sparkplug619/esp32_xiaomi_m365/esp32_m365_oled/include/ARIALN9pt7b.h

const uint8_t ARIALN9pt7bBitmaps[] PROGMEM = {
  0xFF, 0xF5, 0x50, 0xC0, 0xBB, 0xAA, 0xA0, 0x12, 0x12, 0x12, 0x22, 0xFF,
  0x24, 0x24, 0x24, 0xFF, 0x44, 0x4C, 0x48, 0x48, 0x20, 0xF3, 0xB5, 0x2A,
  0x14, 0x38, 0x1C, 0x2C, 0x4A, 0x95, 0x2E, 0xCF, 0x08, 0x10, 0x60, 0x92,
  0x22, 0x44, 0x49, 0x09, 0x21, 0x28, 0x19, 0x30, 0x29, 0x09, 0x21, 0x24,
  0x44, 0x88, 0x92, 0x0C, 0x38, 0x36, 0x11, 0x0C, 0x86, 0xC1, 0xC1, 0xC1,
  0xB6, 0x8F, 0x43, 0x21, 0x99, 0xE7, 0x90, 0xF8, 0x25, 0x2D, 0x24, 0x92,
  0x4C, 0x91, 0x20, 0x91, 0x24, 0xC9, 0x24, 0xB4, 0x94, 0x80, 0x23, 0x4C,
  0xE5, 0x00, 0x10, 0x20, 0x47, 0xF1, 0x02, 0x04, 0x00, 0xD6, 0xF0, 0xC0,
  0x11, 0x32, 0x22, 0x24, 0x44, 0x48, 0x80, 0x79, 0x38, 0x61, 0x86, 0x18,
  0x61, 0x86, 0x18, 0x53, 0x78, 0x25, 0xFA, 0x49, 0x24, 0x92, 0x3C, 0xCD,
  0x0A, 0x10, 0x20, 0xC1, 0x86, 0x18, 0x61, 0x83, 0x0F, 0xE0, 0x79, 0x9A,
  0x10, 0x20, 0x41, 0x0F, 0x06, 0x05, 0x0A, 0x16, 0x67, 0x80, 0x04, 0x18,
  0x30, 0xA1, 0x44, 0x89, 0x22, 0xC5, 0xFC, 0x10, 0x20, 0x40, 0x7C, 0x83,
  0x04, 0x0F, 0x99, 0xA1, 0x03, 0x07, 0x0A, 0x16, 0x67, 0x80, 0x38, 0x9A,
  0x14, 0x08, 0x17, 0x33, 0x42, 0x85, 0x0A, 0x12, 0x63, 0x80, 0xFE, 0x08,
  0x30, 0xC1, 0x82, 0x0C, 0x10, 0x20, 0x41, 0x83, 0x06, 0x00, 0x78, 0x9A,
  0x14, 0x28, 0x59, 0x9E, 0x66, 0x85, 0x0E, 0x16, 0x67, 0x80, 0x79, 0x9A,
  0x14, 0x28, 0x50, 0xF3, 0xBB, 0x04, 0x0A, 0x16, 0x47, 0x00, 0xC0, 0x00,
  0xC0, 0xC0, 0x00, 0xD6, 0x02, 0x18, 0x43, 0x08, 0x0C, 0x04, 0x06, 0x02,
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
  {   351,   7,  13,   9,    1,  -12 },   // 0x46 'F'
  {   363,  10,  13,  11,    1,  -12 },   // 0x47 'G'
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

const GFXfont ARIALN9pt7b PROGMEM = {
  (uint8_t  *)ARIALN9pt7bBitmaps,
  (GFXglyph *)ARIALN9pt7bGlyphs,
  0x20, 0x7E, 21 };

// Approx. 1614 bytes
