sparkplug619/esp32_xiaomi_m365/esp32_m365_oled/include/ARIALNB18pt7b.h

const uint8_t ARIALNB18pt7bBitmaps[] PROGMEM = {
  0xFF, 0xFF, 0xFF, 0xFF, 0xFF, 0xEE, 0xEE, 0xEE, 0xEE, 0x60, 0x0F, 0xFF,
  0xF0, 0xF3, 0xFC, 0xFF, 0x3F, 0xCF, 0xF3, 0xFC, 0xFF, 0x3F, 0x8F, 0xE1,
  0xC0, 0x07, 0x1E, 0x07, 0x1E, 0x07, 0x1C, 0x07, 0x1C, 0x07, 0x1C, 0x0F,
  0x1C, 0xFF, 0xFF, 0xFF, 0xFF, 0xFF, 0xFF, 0xFF, 0xFF, 0x0E, 0x38, 0x1E,
  0x38, 0x1C, 0x78, 0x1C, 0x70, 0x1C, 0x70, 0xFF, 0xFF, 0xFF, 0xFF, 0xFF,
  0xFF, 0xFF, 0xFF, 0x38, 0xE0, 0x38, 0xE0, 0x38, 0xE0, 0x78, 0xE0, 0x70,
  0xE0, 0x71, 0xE0, 0x03, 0x00, 0x0C, 0x00, 0xFC, 0x07, 0xF8, 0x3F, 0xF1,
  0xFF, 0xC7, 0xBF, 0x9C, 0xDE, 0x73, 0x61, 0xCC, 0x07, 0xB0, 0x1F, 0xC0,
  0x7F, 0x00, 0xFF, 0x81, 0xFF, 0x03, 0xFE, 0x03, 0xF8, 0x0D, 0xE0, 0x33,
  0xCC, 0xCF, 0xF3, 0x3F, 0xCC, 0xF7, 0xB7, 0x9F, 0xFE, 0x3F, 0xF0, 0xFF,
  0x80, 0xFC, 0x00, 0xC0, 0x03, 0x00, 0x0C, 0x00, 0x1E, 0x00, 0xC0, 0x7E,
  0x03, 0x81, 0xFE, 0x07, 0x03, 0x9C, 0x1C, 0x0E, 0x38, 0x38, 0x1C, 0x70,
  0xE0, 0x38, 0xE1, 0xC0, 0x71, 0xC7, 0x00, 0xE3, 0x8E, 0x00, 0xE7, 0x18,
  0x01, 0xFE, 0x70, 0x01, 0xF8, 0xE0, 0x01, 0xE3, 0x87, 0x80, 0x07, 0x3F,
  0x80, 0x1C, 0x7F, 0x00, 0x39, 0xE7, 0x00, 0x63, 0x8E, 0x01, 0xC7, 0x1C,
  0x03, 0x8E, 0x38, 0x0E, 0x1C, 0x70, 0x1C, 0x38, 0xE0, 0x70, 0x7B, 0xC0,
  0xE0, 0x7F, 0x83, 0x80, 0xFE, 0x07, 0x00, 0x78, 0x03, 0xE0, 0x01, 0xFF,
  0x00, 0x3F, 0xE0, 0x0F, 0xFE, 0x01, 0xE3, 0xC0, 0x3C, 0x38, 0x07, 0x87,
  0x00, 0xF9, 0xE0, 0x0F, 0xF8, 0x01, 0xFF, 0x00, 0x1F, 0xC0, 0x07, 0xF0,
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
  {  1379,  14,  25,  18,    2,  -24 },   // 0x46 'F'
  {  1423,  20,  25,  22,    1,  -24 },   // 0x47 'G'
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

const GFXfont ARIALNB18pt7b PROGMEM = {
  (uint8_t  *)ARIALNB18pt7bBitmaps,
  (GFXglyph *)ARIALNB18pt7bGlyphs,
  0x20, 0x7E, 40 };

// Approx. 4345 bytes
