sparkplug619/esp32_xiaomi_m365/esp32_m365_oled/include/ARIALNB9pt7b.h

const uint8_t ARIALNB9pt7bBitmaps[] PROGMEM = {
  0xFF, 0xED, 0x92, 0x48, 0x6C, 0xDE, 0xF7, 0xBD, 0x80, 0x13, 0x32, 0x32,
  0xFF, 0xFF, 0x26, 0x26, 0x64, 0xFF, 0xFF, 0x6C, 0x4C, 0x48, 0x10, 0xF3,
  0xF6, 0xED, 0x1A, 0x3C, 0x3E, 0x1C, 0x2E, 0x5E, 0xEF, 0xCF, 0x04, 0x08,
  0x61, 0x96, 0x22, 0x44, 0x49, 0x89, 0x21, 0x6C, 0x19, 0x30, 0x6D, 0x09,
  0x21, 0x24, 0x64, 0x88, 0xD3, 0x0C, 0x3C, 0x3F, 0x19, 0x8C, 0xC7, 0xC1,
  0xE1, 0xE1, 0xFB, 0xCF, 0x63, 0xB1, 0xDF, 0xF7, 0x98, 0xFF, 0xC0, 0x2D,
  0xAD, 0xB6, 0xDB, 0x6C, 0x9B, 0x20, 0x46, 0x62, 0x33, 0x33, 0x33, 0x33,
  0x32, 0x66, 0x40, 0x21, 0x3E, 0x67, 0x28, 0x30, 0x60, 0xC1, 0x8F, 0xFF,
  0xCC, 0x18, 0x30, 0x60, 0xF5, 0x80, 0xFF, 0xF0, 0x13, 0x32, 0x26, 0x66,
  0x44, 0xCC, 0xC0, 0x79, 0xFC, 0xF3, 0xCF, 0x3C, 0xF3, 0xCF, 0x3C, 0xDF,
  0x78, 0x18, 0xCE, 0xFD, 0xCC, 0x63, 0x18, 0xC6, 0x31, 0x80, 0x3C, 0xFD,
  0x9B, 0x30, 0x60, 0xC3, 0x8E, 0x38, 0x61, 0xC3, 0xFF, 0xE0, 0x79, 0xFB,
  0x36, 0x60, 0xC7, 0x0F, 0x06, 0x0F, 0x9F, 0x37, 0xE7, 0x80, 0x06, 0x0E,
  0x1E, 0x1E, 0x36, 0x36, 0x66, 0x46, 0xFF, 0xFF, 0x06, 0x06, 0x06, 0x7C,
  0xF9, 0x06, 0x0F, 0x9F, 0xB3, 0x03, 0x07, 0x8F, 0x37, 0xE7, 0x80, 0x38,
  0xFB, 0x36, 0x0C, 0x1F, 0x3F, 0x67, 0xC7, 0x8F, 0x33, 0xE3, 0x80, 0xFF,
  0xFC, 0x30, 0xC1, 0x83, 0x0C, 0x18, 0x30, 0xC1, 0x83, 0x06, 0x00, 0x79,
  0xFB, 0x36, 0x6C, 0xCF, 0x1F, 0x66, 0xC7, 0x8F, 0x37, 0xE7, 0x80, 0x3C,
  0x7C, 0x66, 0xC6, 0xC6, 0x67, 0x7F, 0x3F, 0x06, 0x06, 0x66, 0x7C, 0x38,
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
  {   374,   7,  13,   9,    1,  -12 },   // 0x46 'F'
  {   386,  10,  13,  11,    1,  -12 },   // 0x47 'G'
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

const GFXfont ARIALNB9pt7b PROGMEM = {
  (uint8_t  *)ARIALNB9pt7bBitmaps,
  (GFXglyph *)ARIALNB9pt7bGlyphs,
  0x20, 0x7E, 21 };

// Approx. 1670 bytes
