sparkplug619/esp32_xiaomi_m365/esp32_m365_oled/include/ariblk42pt7b.h

const uint8_t ariblk42pt7bBitmaps[] PROGMEM = {
  0xFF, 0xFF, 0xFF, 0xFF, 0xFF, 0xFF, 0xFF, 0xFF, 0xFF, 0xFF, 0xFF, 0xFF,
  0xFF, 0xFF, 0xFF, 0xFF, 0xFF, 0xFF, 0xFF, 0xFF, 0xFF, 0xFF, 0xFF, 0xFF,
  0xFF, 0xFF, 0xFF, 0xFF, 0xFF, 0xFF, 0xFF, 0xFF, 0xFF, 0xFF, 0xFF, 0xFF,
  0xFF, 0xFF, 0xDF, 0xFF, 0xEF, 0xFF, 0xF7, 0xFF, 0xFB, 0xFF, 0xF9, 0xFF,
  0xFC, 0xFF, 0xFE, 0x7F, 0xFF, 0x3F, 0xFF, 0x8F, 0xFF, 0xC7, 0xFF, 0xE3,
  0xFF, 0xF1, 0xFF, 0xF0, 0xFF, 0xF8, 0x7F, 0xFC, 0x3F, 0xFE, 0x1F, 0xFF,
  0x0F, 0xFF, 0x83, 0xFF, 0xC1, 0xFF, 0xE0, 0xFF, 0xE0, 0x7F, 0xF0, 0x3F,
  0xF8, 0x1F, 0xFC, 0x00, 0x00, 0x00, 0x00, 0x00, 0x00, 0x00, 0x00, 0x03,
  0xFF, 0xFD, 0xFF, 0xFE, 0xFF, 0xFF, 0x7F, 0xFF, 0xBF, 0xFF, 0xDF, 0xFF,
  0xEF, 0xFF, 0xF7, 0xFF, 0xFB, 0xFF, 0xFD, 0xFF, 0xFE, 0xFF, 0xFF, 0x7F,
  0xFF, 0xBF, 0xFF, 0xDF, 0xFF, 0xE0, 0xFF, 0xFF, 0x8F, 0xFF, 0xFF, 0xFF,
  0xFC, 0x7F, 0xFF, 0xFF, 0xFF, 0xE3, 0xFF, 0xFF, 0xFF, 0xFF, 0x1F, 0xFF,
  0xFF, 0xFF, 0xF8, 0xFF, 0xFF, 0xFF, 0xFF, 0xC7, 0xFF, 0xFF, 0xFF, 0xFE,
  0x3F, 0xFF, 0xFF, 0xFF, 0xF1, 0xFF, 0xFF, 0xFF, 0xFF, 0x8F, 0xFF, 0xFF,
  0xFF, 0xFC, 0x7F, 0xFF, 0xDF, 0xFF, 0xE1, 0xFF, 0xFE, 0xFF, 0xFE, 0x0F,
  0xFF, 0xE7, 0xFF, 0xF0, 0x7F, 0xFF, 0x3F, 0xFF, 0x83, 0xFF, 0xF9, 0xFF,
  0xFC, 0x1F, 0xFF, 0xC7, 0xFF, 0xC0, 0x7F, 0xFC, 0x3F, 0xFE, 0x03, 0xFF,
  0xE1, 0xFF, 0xF0, 0x1F, 0xFF, 0x0F, 0xFF, 0x80, 0xFF, 0xF8, 0x3F, 0xFC,
  0x03, 0xFF, 0xC1, 0xFF, 0xC0, 0x1F, 0xFC, 0x0F, 0xFE, 0x00, 0xFF, 0xE0,
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
  { 10763,  45,  59,  55,    6,  -58 },   // 0x46 'F'
  { 11095,  60,  61,  68,    4,  -59 },   // 0x47 'G'
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

const GFXfont ariblk42pt7b PROGMEM = {
  (uint8_t  *)ariblk42pt7bBitmaps,
  (GFXglyph *)ariblk42pt7bGlyphs,
  0x20, 0x7E, 116 };

// Approx. 29433 bytes
