sparkplug619/esp32_xiaomi_m365/esp32_m365_oled/src/secrets.h

#ifndef SECRETS_h
#define SECRETS_h

//Wifi - CHANGE IT TO YOUR OWN SETTINGS!!!
    #define maxssids 1
    #define ssid1 "yourssid"
    #define password1 "yourpassphrase"
    #define ssid2 "..."
    #define password2 "..."
    #define ssid3 "..."
    #define password3 "..."

//SSID/Pass for Access-Point Mode - CHANGE IT TO YOUR OWN SEQUENCE!!!
    #define ap_ssid "m365oled"
    #define ap_password "appassword"

//Over The Air Firmwareupdates - password - CHANGE IT TO YOUR OWN SEQUENCE!!!
    #define OTApwd "yourotapassword"

#endif
