sparkplug619/esp32_xiaomi_m365/esp32_m365_oled/src/esp32-hal-patched.h

/*
 Arduino.h - Main include file for the Arduino SDK
 Copyright (c) 2005-2013 Arduino Team.  All right reserved.

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
 You should have received a copy of the GNU Lesser General Public
 License along with this library; if not, write to the Free Software
 Foundation, Inc., 51 Franklin St, Fifth Floor, Boston, MA  02110-1301  USA
 */

#ifndef HAL_ESP32_HAL_H_
#define HAL_ESP32_HAL_H_

#ifdef __cplusplus
extern "C" {
#endif

#include <stdint.h>
#include <stdbool.h>
#include <stdio.h>
#include <stdlib.h>
#include <stdarg.h>
#include <inttypes.h>
#include <string.h>
#include <math.h>
#include "sdkconfig.h"
#include "esp_system.h"

#ifndef F_CPU
#define F_CPU (CONFIG_ESP32_DEFAULT_CPU_FREQ_MHZ * 1000000U)
#endif

//forward declaration from freertos/portmacro.h
void vPortYield(void);
void yield(void);
#define optimistic_yield(u)

#define ESP_REG(addr) *((volatile uint32_t *)(addr))
#define NOP() asm volatile ("nop")

#include "esp32-hal-log.h"
#include "esp32-hal-matrix.h"
#include "esp32-hal-uart-patched.h"
#include "esp32-hal-gpio.h"
#include "esp32-hal-touch.h"
#include "esp32-hal-dac.h"
#include "esp32-hal-adc.h"
#include "esp32-hal-spi.h"
#include "esp32-hal-i2c.h"
#include "esp32-hal-ledc.h"
#include "esp32-hal-sigmadelta.h"
#include "esp32-hal-timer.h"
#include "esp32-hal-bt.h"
#include "esp32-hal-psram.h"

#ifndef BOARD_HAS_PSRAM
#ifdef CONFIG_SPIRAM_SUPPORT
#undef CONFIG_SPIRAM_SUPPORT
#endif
#endif

//returns chip temperature in Celsius
float temperatureRead();

unsigned long micros();
unsigned long millis();
void delay(uint32_t);
void delayMicroseconds(uint32_t us);

#if !CONFIG_ESP32_PHY_AUTO_INIT
void arduino_phy_init();
#endif

#if !CONFIG_AUTOSTART_ARDUINO
void initArduino();
#endif

#ifdef __cplusplus
}
#endif

#endif /* HAL_ESP32_HAL_H_ */
